sparkfun/SparkFun_Digi_XBee_Explorer_USB-C/docs/22043/Resized/22043- XBee Explorer USB-C- 04.jpg

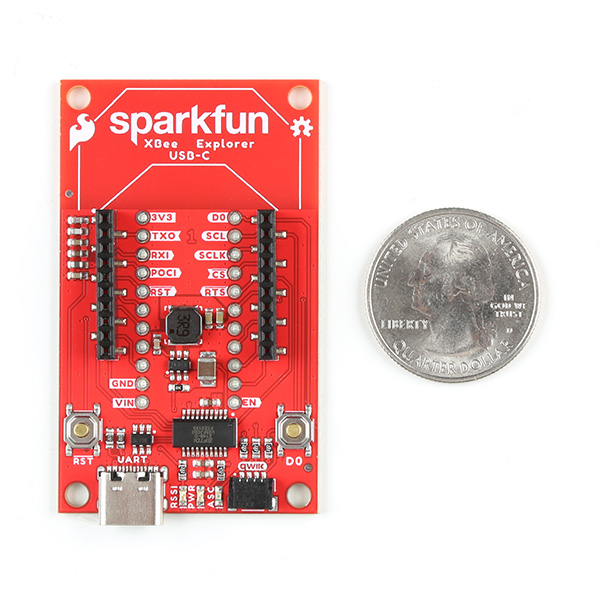
docs/22043/Resized/22043- XBee Explorer USB-C- 04.jpg
